ID6763Fall2016/TransitNotifier_GreenDinosaur/Photos/2016-10-24 17.50.48.jpg

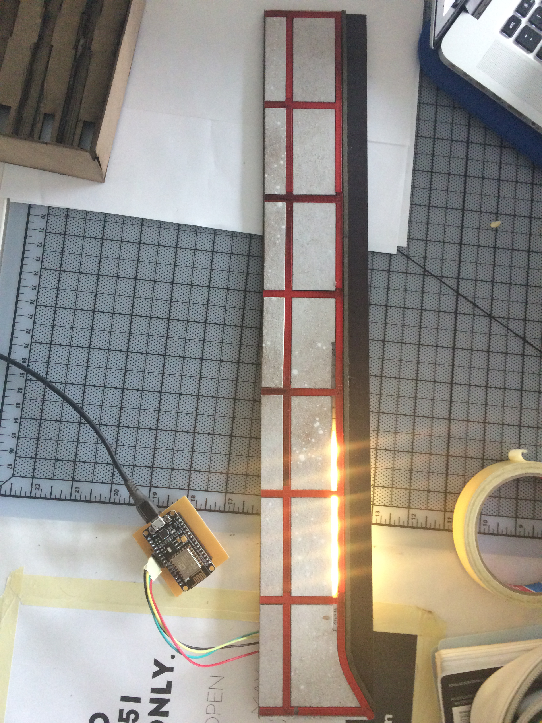
Photos/2016-10-24 17.50.48.jpg
