ID6763Fall2016/TransitNotifier_GreenDinosaur/Photos/2016-10-25 11.32.20.jpg

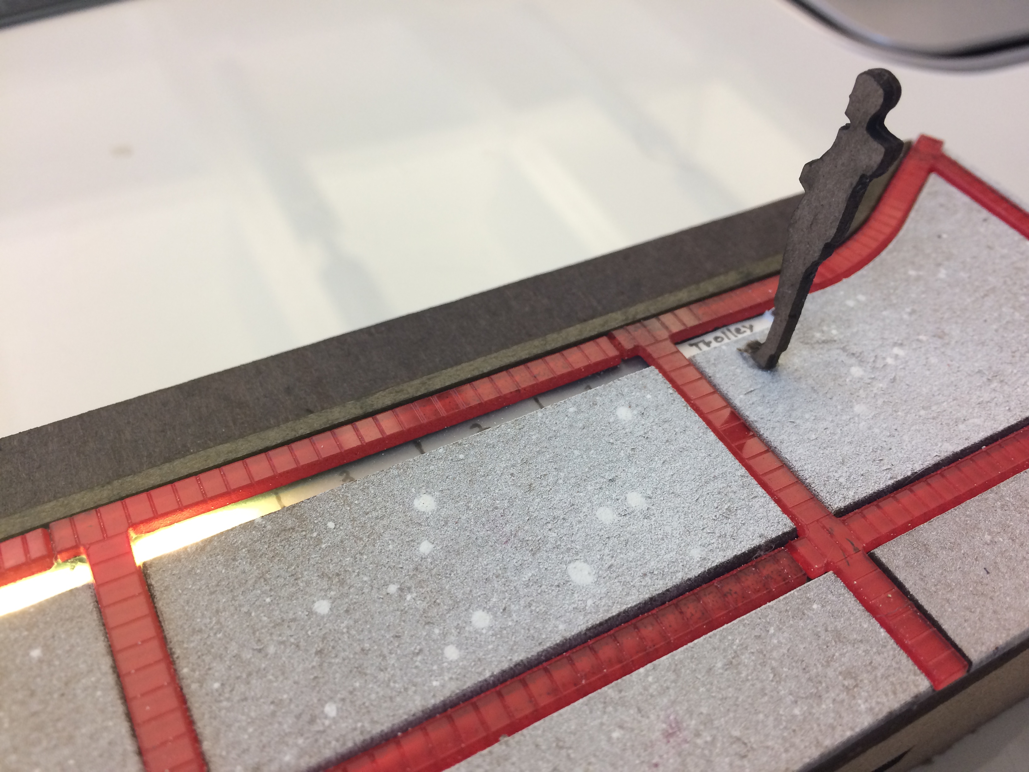
Photos/2016-10-25 11.32.20.jpg
