ID6763Fall2016/TransitNotifier_GreenDinosaur/Photos/IMG_2228.JPG

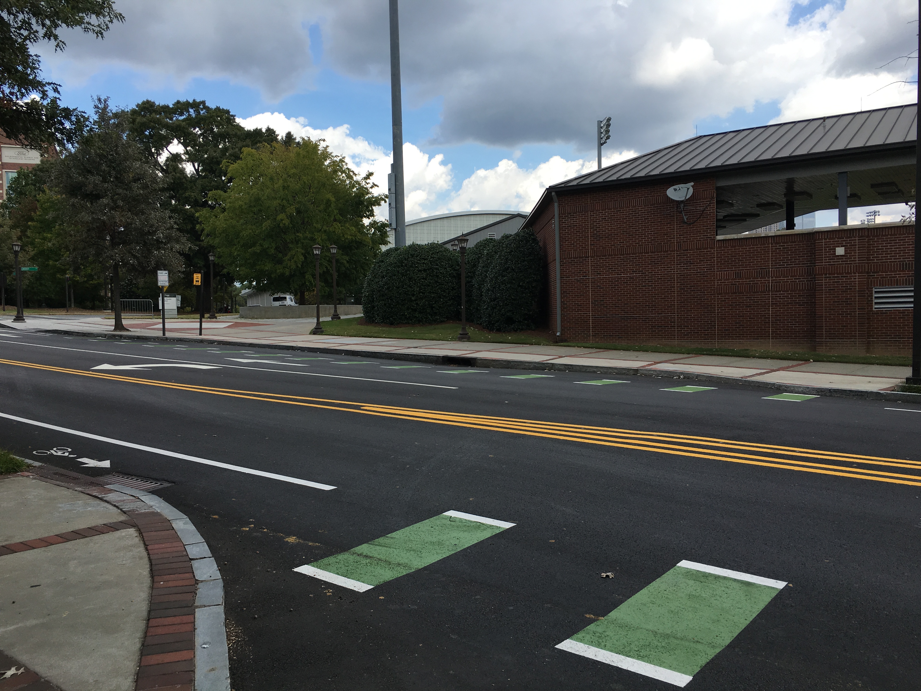
Photos/IMG_2228.JPG
