ID6763Fall2016/TransitNotifier_GreenDinosaur/Photos/IMG_2230.JPG

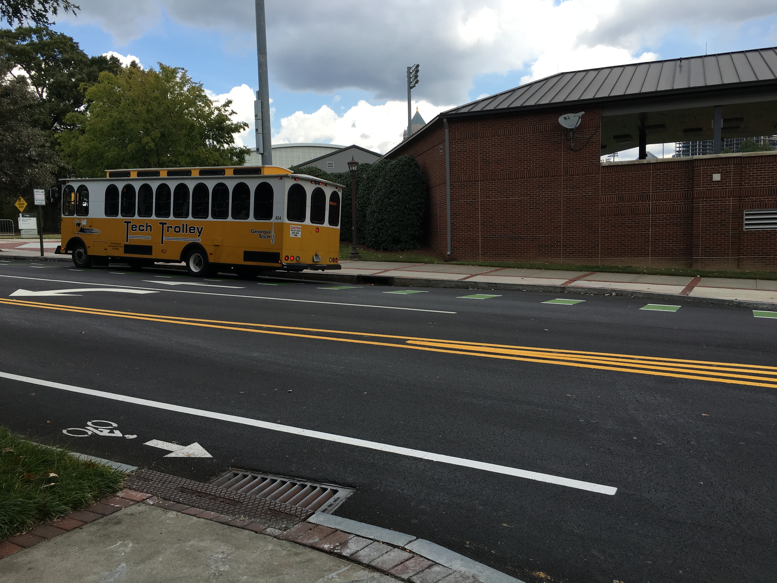
Photos/IMG_2230.JPG
