ID6763Fall2016/TransitNotifier_GreenDinosaur/Photos/pcb.png

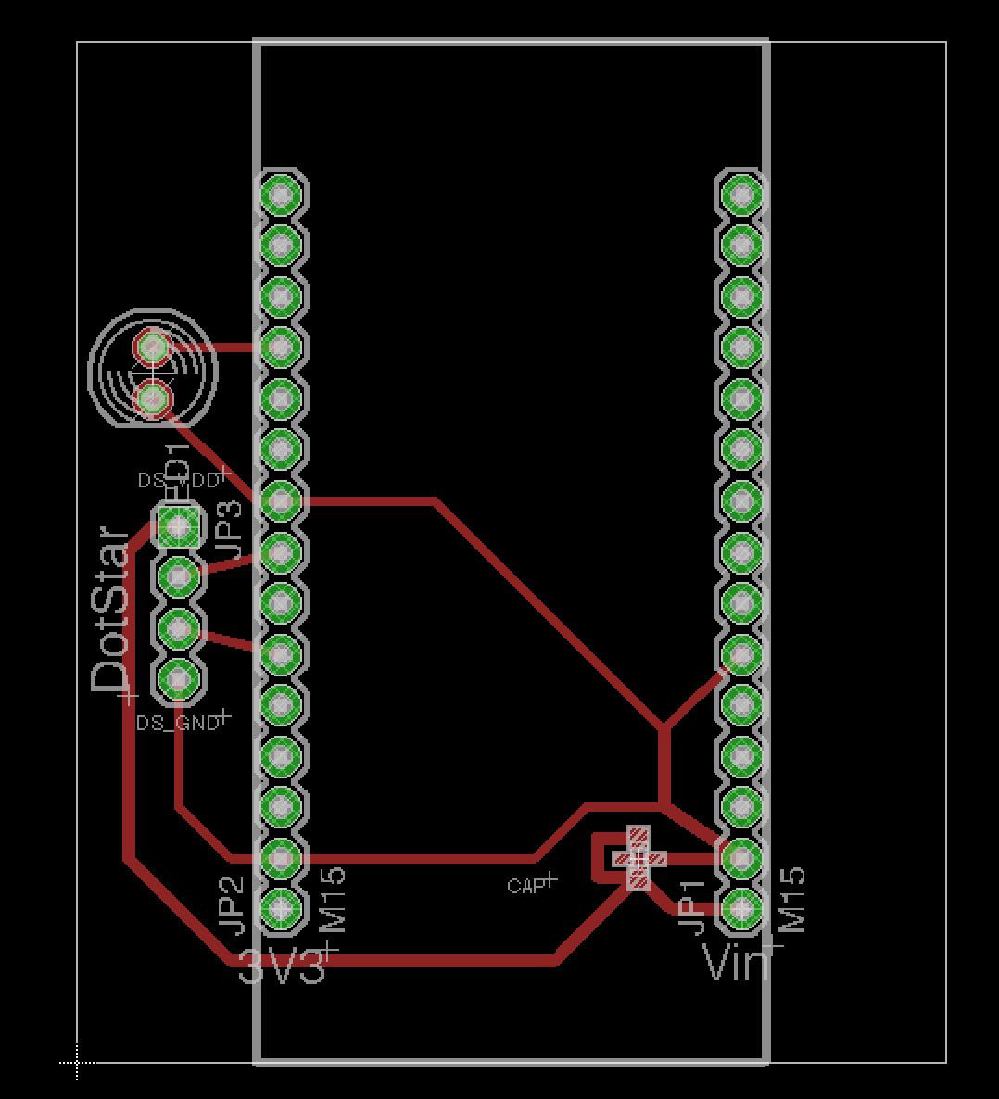
Photos/pcb.png
